krishnaverma24/ESP32-4Layer-PCB-Design/1781695710124.jpg

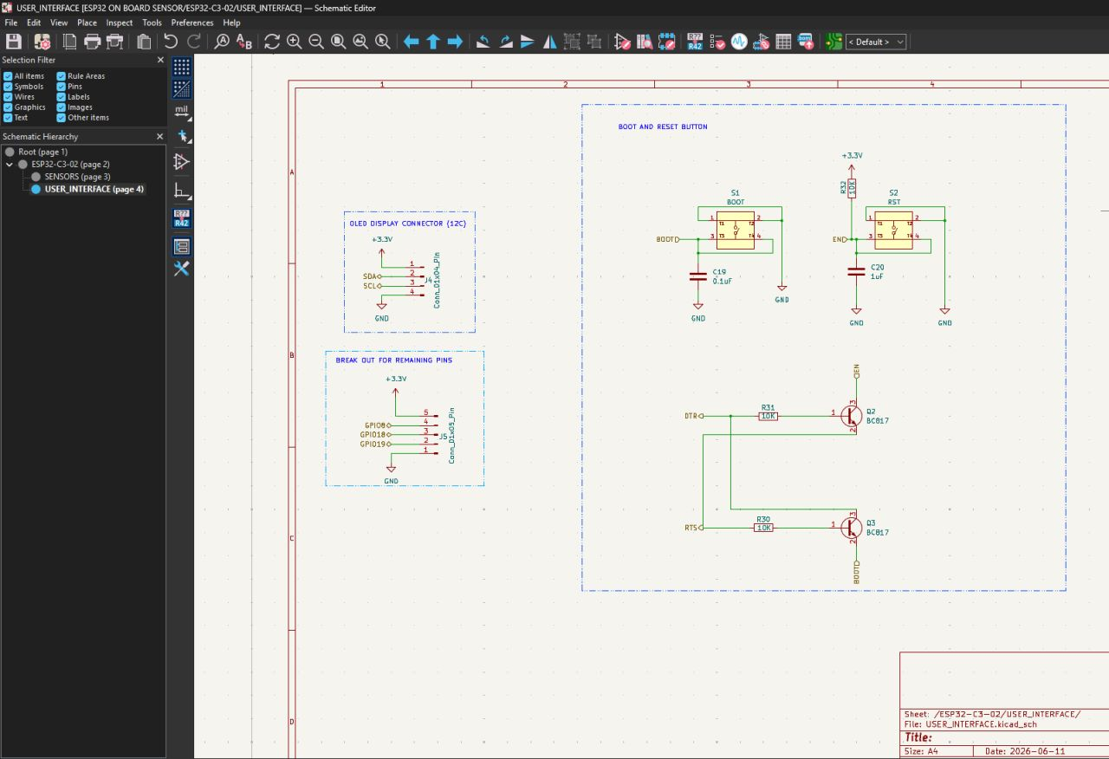
1781695710124.jpg
