krishnaverma24/ESP32-4Layer-PCB-Design/1781695710553.jpg

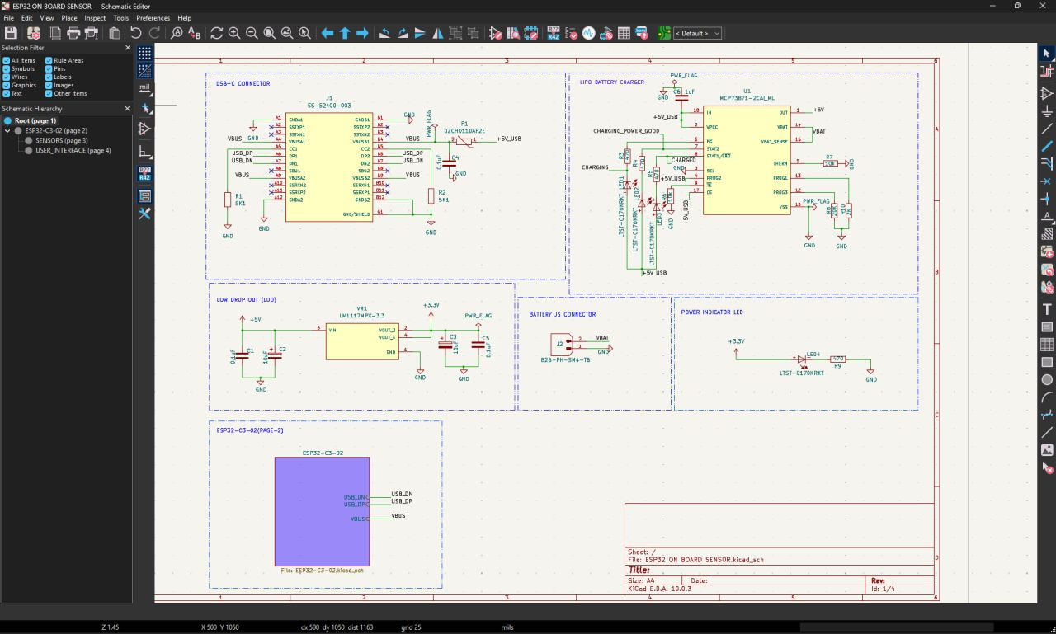
1781695710553.jpg
