krishnaverma24/ESP32-4Layer-PCB-Design/1781695710832.jpg

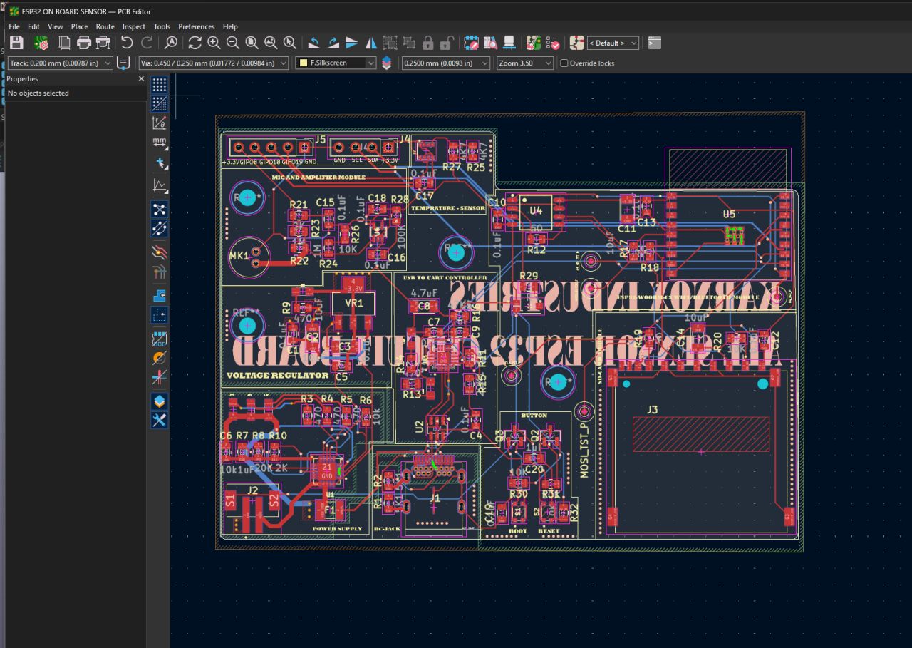
1781695710832.jpg
