krishnaverma24/ESP32-4Layer-PCB-Design/1781695710928.jpg

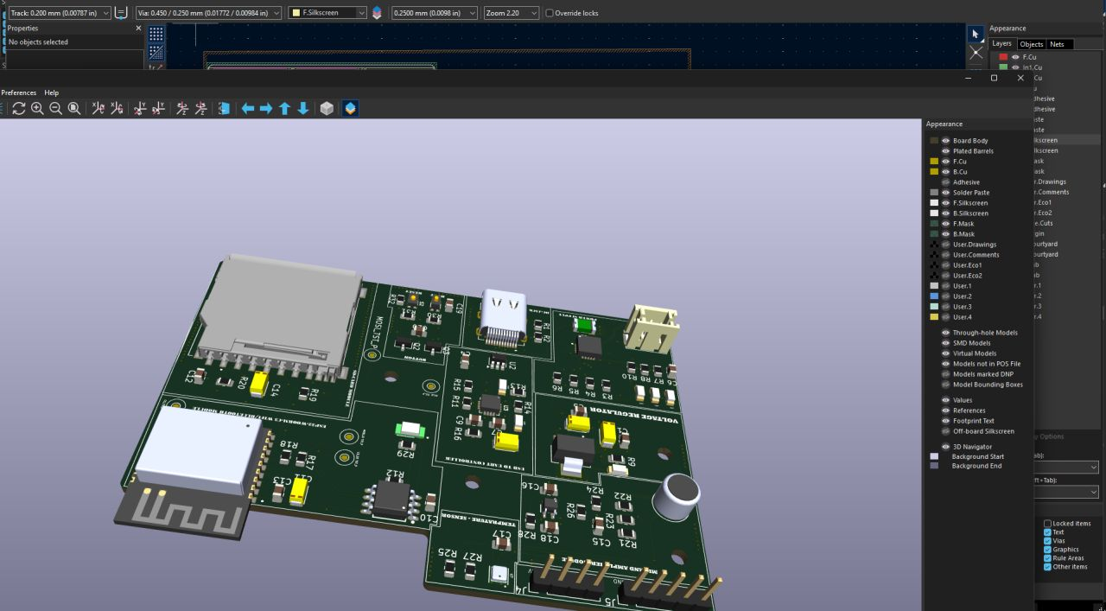
1781695710928.jpg
