krishnaverma24/ESP32-4Layer-PCB-Design/1781695711047.jpg

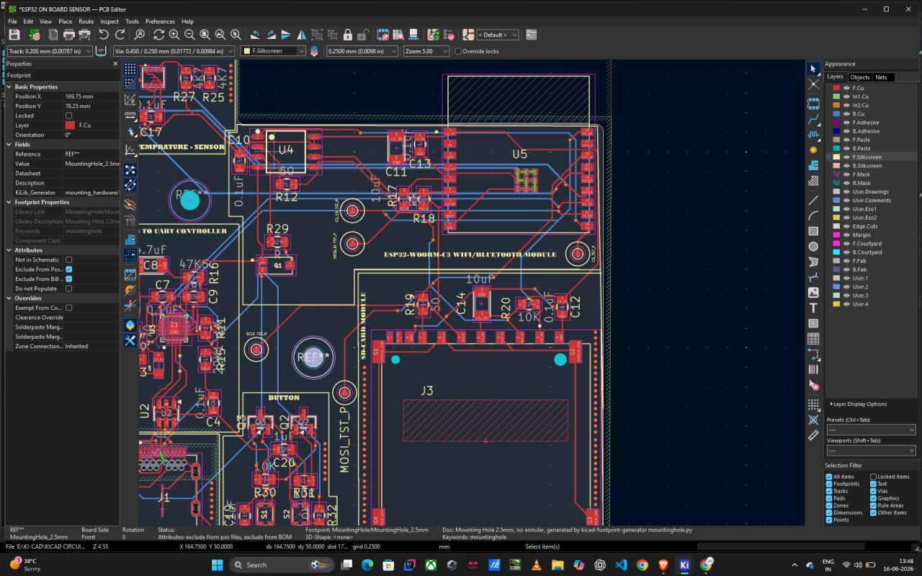
1781695711047.jpg
