krishnaverma24/ESP32-4Layer-PCB-Design/1781695711110.jpg

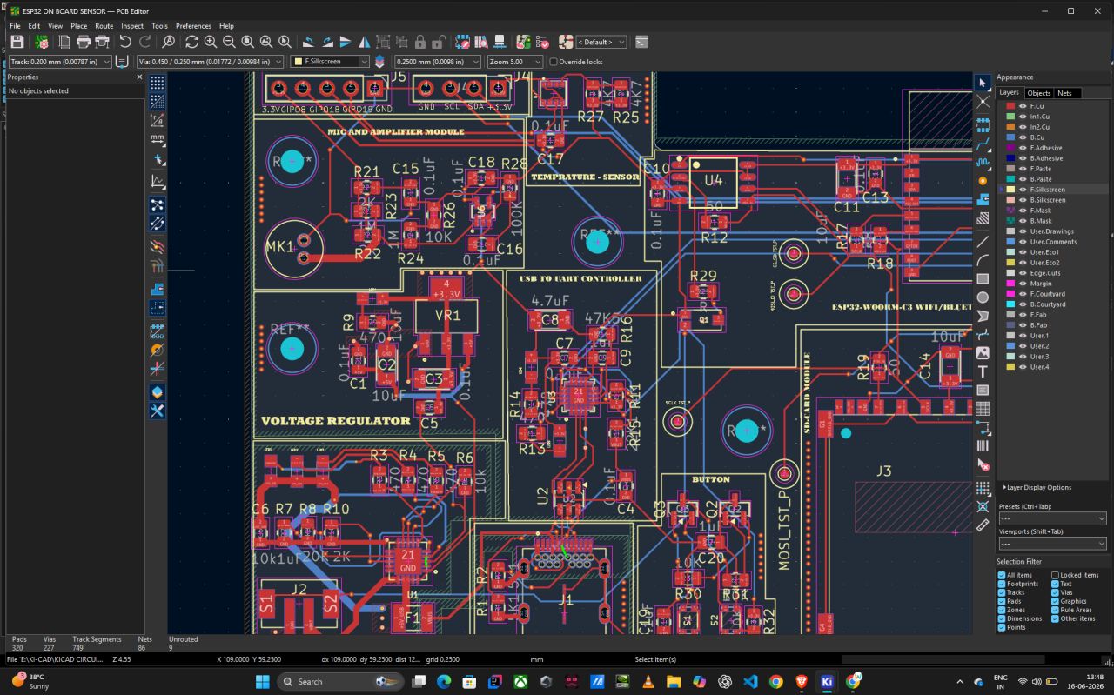
1781695711110.jpg
