krishnaverma24/ESP32-4Layer-PCB-Design/1781695711161.jpg

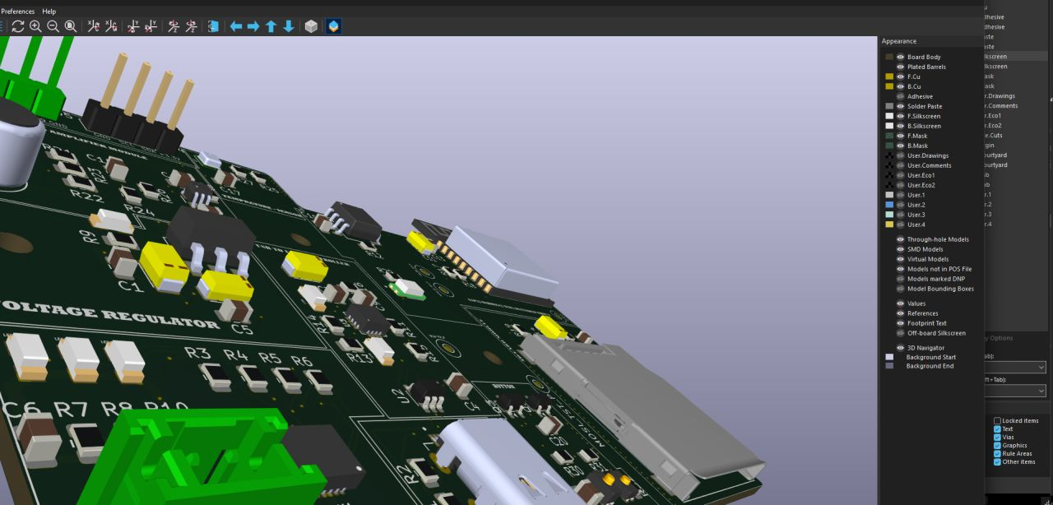
1781695711161.jpg
